Dudestin/tinyEtherDeveloper/RTL_project/L2-Switch/L2-Switch_watcherInst.v

module CW_TOP_WRAPPER(jtdi, jtck, jrstn, jscan, jshift, jupdate, jtdo, non_bus_din, bus_din, trig_clk, wt_ce, wt_en, wt_addr);
	localparam DEFAULT_CTRL_REG_LEN = 298;
	localparam DEFAULT_STAT_REG_LEN = 18;
	localparam DEFAULT_STOP_LEN = 682;
	localparam DEFAULT_NON_BUS_NODE_NUM = 2;
	localparam DEFAULT_BUS_NODE_NUM = 15;
	localparam DEFAULT_BUS_NUM = 4;
	localparam DEFAULT_BUS1_WIDTH = 4;
	localparam DEFAULT_BUS2_WIDTH = 4;
	localparam DEFAULT_BUS3_WIDTH = 4;
	localparam DEFAULT_BUS4_WIDTH = 3;
	input jtdi;
	input jtck;
	input jrstn;
	input [1:0] jscan;
	input jshift;
	input jupdate;
	output [1:0] jtdo;
	input trig_clk;
	input [DEFAULT_NON_BUS_NODE_NUM-1:0] non_bus_din;
	input [DEFAULT_BUS_NODE_NUM-1:0] bus_din;
	output wt_ce;
	output wt_en;
	output [15:0] wt_addr;

	cwc_top #(.BUS1_WIDTH(DEFAULT_BUS1_WIDTH), .BUS2_WIDTH(DEFAULT_BUS2_WIDTH), .BUS3_WIDTH(DEFAULT_BUS3_WIDTH), .BUS4_WIDTH(DEFAULT_BUS4_WIDTH), .CTRL_REG_LEN(DEFAULT_CTRL_REG_LEN), .STAT_REG_LEN(DEFAULT_STAT_REG_LEN), .STOP_LEN(DEFAULT_STOP_LEN), .NON_BUS_NODE_NUM(DEFAULT_NON_BUS_NODE_NUM), .BUS_NODE_NUM(DEFAULT_BUS_NODE_NUM), .BUS_NUM(DEFAULT_BUS_NUM))
	 wrapper_cwc_top(
		.jtdi(jtdi),
		.jtck(jtck),
		.jrstn(jrstn),
		.jscan(jscan),
		.jshift(jshift),
		.jupdate(jupdate),
		.jtdo(jtdo),
		.non_bus_din(non_bus_din),
		.bus_din(bus_din),
		.trig_clk(trig_clk),
		.wt_ce(wt_ce),
		.wt_en(wt_en),
		.wt_addr(wt_addr)
	);
endmodule
