Dudestin/tinyEtherDeveloper/RTL_project/common/al_ip/CTRL_FRAME_RAM_sim.v

// Verilog netlist created by TD v4.4.433
// Thu Aug 11 10:00:17 2022

`timescale 1ns / 1ps
module CTRL_FRAME_FIFO  // al_ip/CTRL_FRAME_FIFO.v(14)
  (
  addra,
  addrb,
  clka,
  clkb,
  dia,
  dib,
  rsta,
  rstb,
  wea,
  web,
  doa,
  dob
  );

  input [9:0] addra;  // al_ip/CTRL_FRAME_FIFO.v(25)
  input [9:0] addrb;  // al_ip/CTRL_FRAME_FIFO.v(26)
  input clka;  // al_ip/CTRL_FRAME_FIFO.v(29)
  input clkb;  // al_ip/CTRL_FRAME_FIFO.v(30)
  input [31:0] dia;  // al_ip/CTRL_FRAME_FIFO.v(23)
  input [31:0] dib;  // al_ip/CTRL_FRAME_FIFO.v(24)
  input rsta;  // al_ip/CTRL_FRAME_FIFO.v(31)
  input rstb;  // al_ip/CTRL_FRAME_FIFO.v(32)
  input [3:0] wea;  // al_ip/CTRL_FRAME_FIFO.v(27)
  input [3:0] web;  // al_ip/CTRL_FRAME_FIFO.v(28)
  output [31:0] doa;  // al_ip/CTRL_FRAME_FIFO.v(19)
  output [31:0] dob;  // al_ip/CTRL_FRAME_FIFO.v(20)


  EG_PHY_CONFIG #(
    .DONE_PERSISTN("ENABLE"),
    .INIT_PERSISTN("ENABLE"),
    .JTAG_PERSISTN("DISABLE"),
    .PROGRAMN_PERSISTN("DISABLE"))
    config_inst ();
  // address_offset=0;data_offset=0;depth=1024;width=8;num_section=1;width_per_section=8;section_size=32;working_depth=1024;working_width=9;address_step=1;bytes_in_per_section=1;
  EG_PHY_BRAM #(
    .CEAMUX("1"),
    .CEBMUX("1"),
    .CSA0("1"),
    .CSA1("1"),
    .CSA2("1"),
    .CSB0("1"),
    .CSB1("1"),
    .CSB2("1"),
    .DATA_WIDTH_A("9"),
    .DATA_WIDTH_B("9"),
    .INITP_00(256'h0000000000000000000000000000000000000000000000000000000000000000),
    .INITP_01(256'h0000000000000000000000000000000000000000000000000000000000000000),
    .INITP_02(256'h0000000000000000000000000000000000000000000000000000000000000000),
    .INITP_03(256'h0000000000000000000000000000000000000000000000000000000000000000),
    .INIT_00(256'h0000000000000000000000000000000000000000000000000000000000000000),
    .INIT_01(256'h0000000000000000000000000000000000000000000000000000000000000000),
    .INIT_02(256'h0000000000000000000000000000000000000000000000000000000000000000),
    .INIT_03(256'h0000000000000000000000000000000000000000000000000000000000000000),
    .INIT_04(256'h0000000000000000000000000000000000000000000000000000000000000000),
    .INIT_05(256'h0000000000000000000000000000000000000000000000000000000000000000),
    .INIT_06(256'h0000000000000000000000000000000000000000000000000000000000000000),
    .INIT_07(256'h0000000000000000000000000000000000000000000000000000000000000000),
    .INIT_08(256'h0000000000000000000000000000000000000000000000000000000000000000),
    .INIT_09(256'h0000000000000000000000000000000000000000000000000000000000000000),
    .INIT_0A(256'h0000000000000000000000000000000000000000000000000000000000000000),
    .INIT_0B(256'h0000000000000000000000000000000000000000000000000000000000000000),
    .INIT_0C(256'h0000000000000000000000000000000000000000000000000000000000000000),
    .INIT_0D(256'h0000000000000000000000000000000000000000000000000000000000000000),
    .INIT_0E(256'h0000000000000000000000000000000000000000000000000000000000000000),
    .INIT_0F(256'h0000000000000000000000000000000000000000000000000000000000000000),
    .INIT_10(256'h0000000000000000000000000000000000000000000000000000000000000000),
    .INIT_11(256'h0000000000000000000000000000000000000000000000000000000000000000),
    .INIT_12(256'h0000000000000000000000000000000000000000000000000000000000000000),
    .INIT_13(256'h0000000000000000000000000000000000000000000000000000000000000000),
    .INIT_14(256'h0000000000000000000000000000000000000000000000000000000000000000),
    .INIT_15(256'h0000000000000000000000000000000000000000000000000000000000000000),
    .INIT_16(256'h0000000000000000000000000000000000000000000000000000000000000000),
    .INIT_17(256'h0000000000000000000000000000000000000000000000000000000000000000),
    .INIT_18(256'h0000000000000000000000000000000000000000000000000000000000000000),
    .INIT_19(256'h0000000000000000000000000000000000000000000000000000000000000000),
    .INIT_1A(256'h0000000000000000000000000000000000000000000000000000000000000000),
    .INIT_1B(256'h0000000000000000000000000000000000000000000000000000000000000000),
    .INIT_1C(256'h0000000000000000000000000000000000000000000000000000000000000000),
    .INIT_1D(256'h0000000000000000000000000000000000000000000000000000000000000000),
    .INIT_1E(256'h0000000000000000000000000000000000000000000000000000000000000000),
    .INIT_1F(256'h0000000000000000000000000000000000000000000000000000000000000000),
    .MODE("DP8K"),
    .OCEAMUX("0"),
    .OCEBMUX("0"),
    .REGMODE_A("NOREG"),
    .REGMODE_B("NOREG"),
    .RESETMODE("SYNC"),
    .WRITEMODE_A("NORMAL"),
    .WRITEMODE_B("NORMAL"))
    inst_1024x32_sub_000000_000 (
    .addra({addra,3'b111}),
    .addrb({addrb,3'b111}),
    .clka(clka),
    .clkb(clkb),
    .dia({open_n55,dia[7:0]}),
    .dib({open_n56,dib[7:0]}),
    .rsta(rsta),
    .rstb(rstb),
    .wea(wea[0]),
    .web(web[0]),
    .doa({open_n59,doa[7:0]}),
    .dob({open_n60,dob[7:0]}));
  // address_offset=0;data_offset=8;depth=1024;width=8;num_section=1;width_per_section=8;section_size=32;working_depth=1024;working_width=9;address_step=1;bytes_in_per_section=1;
  EG_PHY_BRAM #(
    .CEAMUX("1"),
    .CEBMUX("1"),
    .CSA0("1"),
    .CSA1("1"),
    .CSA2("1"),
    .CSB0("1"),
    .CSB1("1"),
    .CSB2("1"),
    .DATA_WIDTH_A("9"),
    .DATA_WIDTH_B("9"),
    .INITP_00(256'h0000000000000000000000000000000000000000000000000000000000000000),
    .INITP_01(256'h0000000000000000000000000000000000000000000000000000000000000000),
    .INITP_02(256'h0000000000000000000000000000000000000000000000000000000000000000),
    .INITP_03(256'h0000000000000000000000000000000000000000000000000000000000000000),
    .INIT_00(256'h0000000000000000000000000000000000000000000000000000000000000000),
    .INIT_01(256'h0000000000000000000000000000000000000000000000000000000000000000),
    .INIT_02(256'h0000000000000000000000000000000000000000000000000000000000000000),
    .INIT_03(256'h0000000000000000000000000000000000000000000000000000000000000000),
    .INIT_04(256'h0000000000000000000000000000000000000000000000000000000000000000),
    .INIT_05(256'h0000000000000000000000000000000000000000000000000000000000000000),
    .INIT_06(256'h0000000000000000000000000000000000000000000000000000000000000000),
    .INIT_07(256'h0000000000000000000000000000000000000000000000000000000000000000),
    .INIT_08(256'h0000000000000000000000000000000000000000000000000000000000000000),
    .INIT_09(256'h0000000000000000000000000000000000000000000000000000000000000000),
    .INIT_0A(256'h0000000000000000000000000000000000000000000000000000000000000000),
    .INIT_0B(256'h0000000000000000000000000000000000000000000000000000000000000000),
    .INIT_0C(256'h0000000000000000000000000000000000000000000000000000000000000000),
    .INIT_0D(256'h0000000000000000000000000000000000000000000000000000000000000000),
    .INIT_0E(256'h0000000000000000000000000000000000000000000000000000000000000000),
    .INIT_0F(256'h0000000000000000000000000000000000000000000000000000000000000000),
    .INIT_10(256'h0000000000000000000000000000000000000000000000000000000000000000),
    .INIT_11(256'h0000000000000000000000000000000000000000000000000000000000000000),
    .INIT_12(256'h0000000000000000000000000000000000000000000000000000000000000000),
    .INIT_13(256'h0000000000000000000000000000000000000000000000000000000000000000),
    .INIT_14(256'h0000000000000000000000000000000000000000000000000000000000000000),
    .INIT_15(256'h0000000000000000000000000000000000000000000000000000000000000000),
    .INIT_16(256'h0000000000000000000000000000000000000000000000000000000000000000),
    .INIT_17(256'h0000000000000000000000000000000000000000000000000000000000000000),
    .INIT_18(256'h0000000000000000000000000000000000000000000000000000000000000000),
    .INIT_19(256'h0000000000000000000000000000000000000000000000000000000000000000),
    .INIT_1A(256'h0000000000000000000000000000000000000000000000000000000000000000),
    .INIT_1B(256'h0000000000000000000000000000000000000000000000000000000000000000),
    .INIT_1C(256'h0000000000000000000000000000000000000000000000000000000000000000),
    .INIT_1D(256'h0000000000000000000000000000000000000000000000000000000000000000),
    .INIT_1E(256'h0000000000000000000000000000000000000000000000000000000000000000),
    .INIT_1F(256'h0000000000000000000000000000000000000000000000000000000000000000),
    .MODE("DP8K"),
    .OCEAMUX("0"),
    .OCEBMUX("0"),
    .REGMODE_A("NOREG"),
    .REGMODE_B("NOREG"),
    .RESETMODE("SYNC"),
    .WRITEMODE_A("NORMAL"),
    .WRITEMODE_B("NORMAL"))
    inst_1024x32_sub_000000_008 (
    .addra({addra,3'b111}),
    .addrb({addrb,3'b111}),
    .clka(clka),
    .clkb(clkb),
    .dia({open_n69,dia[15:8]}),
    .dib({open_n70,dib[15:8]}),
    .rsta(rsta),
    .rstb(rstb),
    .wea(wea[1]),
    .web(web[1]),
    .doa({open_n73,doa[15:8]}),
    .dob({open_n74,dob[15:8]}));
  // address_offset=0;data_offset=16;depth=1024;width=8;num_section=1;width_per_section=8;section_size=32;working_depth=1024;working_width=9;address_step=1;bytes_in_per_section=1;
  EG_PHY_BRAM #(
    .CEAMUX("1"),
    .CEBMUX("1"),
    .CSA0("1"),
    .CSA1("1"),
    .CSA2("1"),
    .CSB0("1"),
    .CSB1("1"),
    .CSB2("1"),
    .DATA_WIDTH_A("9"),
    .DATA_WIDTH_B("9"),
    .INITP_00(256'h0000000000000000000000000000000000000000000000000000000000000000),
    .INITP_01(256'h0000000000000000000000000000000000000000000000000000000000000000),
    .INITP_02(256'h0000000000000000000000000000000000000000000000000000000000000000),
    .INITP_03(256'h0000000000000000000000000000000000000000000000000000000000000000),
    .INIT_00(256'h0000000000000000000000000000000000000000000000000000000000000000),
    .INIT_01(256'h0000000000000000000000000000000000000000000000000000000000000000),
    .INIT_02(256'h0000000000000000000000000000000000000000000000000000000000000000),
    .INIT_03(256'h0000000000000000000000000000000000000000000000000000000000000000),
    .INIT_04(256'h0000000000000000000000000000000000000000000000000000000000000000),
    .INIT_05(256'h0000000000000000000000000000000000000000000000000000000000000000),
    .INIT_06(256'h0000000000000000000000000000000000000000000000000000000000000000),
    .INIT_07(256'h0000000000000000000000000000000000000000000000000000000000000000),
    .INIT_08(256'h0000000000000000000000000000000000000000000000000000000000000000),
    .INIT_09(256'h0000000000000000000000000000000000000000000000000000000000000000),
    .INIT_0A(256'h0000000000000000000000000000000000000000000000000000000000000000),
    .INIT_0B(256'h0000000000000000000000000000000000000000000000000000000000000000),
    .INIT_0C(256'h0000000000000000000000000000000000000000000000000000000000000000),
    .INIT_0D(256'h0000000000000000000000000000000000000000000000000000000000000000),
    .INIT_0E(256'h0000000000000000000000000000000000000000000000000000000000000000),
    .INIT_0F(256'h0000000000000000000000000000000000000000000000000000000000000000),
    .INIT_10(256'h0000000000000000000000000000000000000000000000000000000000000000),
    .INIT_11(256'h0000000000000000000000000000000000000000000000000000000000000000),
    .INIT_12(256'h0000000000000000000000000000000000000000000000000000000000000000),
    .INIT_13(256'h0000000000000000000000000000000000000000000000000000000000000000),
    .INIT_14(256'h0000000000000000000000000000000000000000000000000000000000000000),
    .INIT_15(256'h0000000000000000000000000000000000000000000000000000000000000000),
    .INIT_16(256'h0000000000000000000000000000000000000000000000000000000000000000),
    .INIT_17(256'h0000000000000000000000000000000000000000000000000000000000000000),
    .INIT_18(256'h0000000000000000000000000000000000000000000000000000000000000000),
    .INIT_19(256'h0000000000000000000000000000000000000000000000000000000000000000),
    .INIT_1A(256'h0000000000000000000000000000000000000000000000000000000000000000),
    .INIT_1B(256'h0000000000000000000000000000000000000000000000000000000000000000),
    .INIT_1C(256'h0000000000000000000000000000000000000000000000000000000000000000),
    .INIT_1D(256'h0000000000000000000000000000000000000000000000000000000000000000),
    .INIT_1E(256'h0000000000000000000000000000000000000000000000000000000000000000),
    .INIT_1F(256'h0000000000000000000000000000000000000000000000000000000000000000),
    .MODE("DP8K"),
    .OCEAMUX("0"),
    .OCEBMUX("0"),
    .REGMODE_A("NOREG"),
    .REGMODE_B("NOREG"),
    .RESETMODE("SYNC"),
    .WRITEMODE_A("NORMAL"),
    .WRITEMODE_B("NORMAL"))
    inst_1024x32_sub_000000_016 (
    .addra({addra,3'b111}),
    .addrb({addrb,3'b111}),
    .clka(clka),
    .clkb(clkb),
    .dia({open_n83,dia[23:16]}),
    .dib({open_n84,dib[23:16]}),
    .rsta(rsta),
    .rstb(rstb),
    .wea(wea[2]),
    .web(web[2]),
    .doa({open_n87,doa[23:16]}),
    .dob({open_n88,dob[23:16]}));
  // address_offset=0;data_offset=24;depth=1024;width=8;num_section=1;width_per_section=8;section_size=32;working_depth=1024;working_width=9;address_step=1;bytes_in_per_section=1;
  EG_PHY_BRAM #(
    .CEAMUX("1"),
    .CEBMUX("1"),
    .CSA0("1"),
    .CSA1("1"),
    .CSA2("1"),
    .CSB0("1"),
    .CSB1("1"),
    .CSB2("1"),
    .DATA_WIDTH_A("9"),
    .DATA_WIDTH_B("9"),
    .INITP_00(256'h0000000000000000000000000000000000000000000000000000000000000000),
    .INITP_01(256'h0000000000000000000000000000000000000000000000000000000000000000),
    .INITP_02(256'h0000000000000000000000000000000000000000000000000000000000000000),
    .INITP_03(256'h0000000000000000000000000000000000000000000000000000000000000000),
    .INIT_00(256'h0000000000000000000000000000000000000000000000000000000000000000),
    .INIT_01(256'h0000000000000000000000000000000000000000000000000000000000000000),
    .INIT_02(256'h0000000000000000000000000000000000000000000000000000000000000000),
    .INIT_03(256'h0000000000000000000000000000000000000000000000000000000000000000),
    .INIT_04(256'h0000000000000000000000000000000000000000000000000000000000000000),
    .INIT_05(256'h0000000000000000000000000000000000000000000000000000000000000000),
    .INIT_06(256'h0000000000000000000000000000000000000000000000000000000000000000),
    .INIT_07(256'h0000000000000000000000000000000000000000000000000000000000000000),
    .INIT_08(256'h0000000000000000000000000000000000000000000000000000000000000000),
    .INIT_09(256'h0000000000000000000000000000000000000000000000000000000000000000),
    .INIT_0A(256'h0000000000000000000000000000000000000000000000000000000000000000),
    .INIT_0B(256'h0000000000000000000000000000000000000000000000000000000000000000),
    .INIT_0C(256'h0000000000000000000000000000000000000000000000000000000000000000),
    .INIT_0D(256'h0000000000000000000000000000000000000000000000000000000000000000),
    .INIT_0E(256'h0000000000000000000000000000000000000000000000000000000000000000),
    .INIT_0F(256'h0000000000000000000000000000000000000000000000000000000000000000),
    .INIT_10(256'h0000000000000000000000000000000000000000000000000000000000000000),
    .INIT_11(256'h0000000000000000000000000000000000000000000000000000000000000000),
    .INIT_12(256'h0000000000000000000000000000000000000000000000000000000000000000),
    .INIT_13(256'h0000000000000000000000000000000000000000000000000000000000000000),
    .INIT_14(256'h0000000000000000000000000000000000000000000000000000000000000000),
    .INIT_15(256'h0000000000000000000000000000000000000000000000000000000000000000),
    .INIT_16(256'h0000000000000000000000000000000000000000000000000000000000000000),
    .INIT_17(256'h0000000000000000000000000000000000000000000000000000000000000000),
    .INIT_18(256'h0000000000000000000000000000000000000000000000000000000000000000),
    .INIT_19(256'h0000000000000000000000000000000000000000000000000000000000000000),
    .INIT_1A(256'h0000000000000000000000000000000000000000000000000000000000000000),
    .INIT_1B(256'h0000000000000000000000000000000000000000000000000000000000000000),
    .INIT_1C(256'h0000000000000000000000000000000000000000000000000000000000000000),
    .INIT_1D(256'h0000000000000000000000000000000000000000000000000000000000000000),
    .INIT_1E(256'h0000000000000000000000000000000000000000000000000000000000000000),
    .INIT_1F(256'h0000000000000000000000000000000000000000000000000000000000000000),
    .MODE("DP8K"),
    .OCEAMUX("0"),
    .OCEBMUX("0"),
    .REGMODE_A("NOREG"),
    .REGMODE_B("NOREG"),
    .RESETMODE("SYNC"),
    .WRITEMODE_A("NORMAL"),
    .WRITEMODE_B("NORMAL"))
    inst_1024x32_sub_000000_024 (
    .addra({addra,3'b111}),
    .addrb({addrb,3'b111}),
    .clka(clka),
    .clkb(clkb),
    .dia({open_n97,dia[31:24]}),
    .dib({open_n98,dib[31:24]}),
    .rsta(rsta),
    .rstb(rstb),
    .wea(wea[3]),
    .web(web[3]),
    .doa({open_n101,doa[31:24]}),
    .dob({open_n102,dob[31:24]}));

endmodule 
