Dudestin/tinyEtherDeveloper/RTL_project/common/al_ip/bram32k_sim.v

// Verilog netlist created by TD v4.4.433
// Tue Jul 26 14:06:52 2022

`timescale 1ns / 1ps
module bram32k  // al_ip/bram32k.v(14)
  (
  addra,
  addrb,
  clka,
  clkb,
  dia,
  dib,
  rsta,
  rstb,
  wea,
  web,
  doa,
  dob
  );

  input [11:0] addra;  // al_ip/bram32k.v(25)
  input [11:0] addrb;  // al_ip/bram32k.v(26)
  input clka;  // al_ip/bram32k.v(29)
  input clkb;  // al_ip/bram32k.v(30)
  input [7:0] dia;  // al_ip/bram32k.v(23)
  input [7:0] dib;  // al_ip/bram32k.v(24)
  input rsta;  // al_ip/bram32k.v(31)
  input rstb;  // al_ip/bram32k.v(32)
  input wea;  // al_ip/bram32k.v(27)
  input web;  // al_ip/bram32k.v(28)
  output [7:0] doa;  // al_ip/bram32k.v(19)
  output [7:0] dob;  // al_ip/bram32k.v(20)


  EG_PHY_CONFIG #(
    .DONE_PERSISTN("ENABLE"),
    .INIT_PERSISTN("ENABLE"),
    .JTAG_PERSISTN("DISABLE"),
    .PROGRAMN_PERSISTN("DISABLE"))
    config_inst ();
  // address_offset=0;data_offset=0;depth=4096;width=8;num_section=1;width_per_section=8;section_size=8;working_depth=4096;working_width=8;address_step=1;bytes_in_per_section=1;
  EG_PHY_BRAM32K #(
    .CSAMUX("1"),
    .CSBMUX("1"),
    .DATA_WIDTH_A("8"),
    .DATA_WIDTH_B("8"),
    .INIT_00(256'h0000000000000000000000000000000000000000000000000000000000000000),
    .INIT_01(256'h0000000000000000000000000000000000000000000000000000000000000000),
    .INIT_02(256'h0000000000000000000000000000000000000000000000000000000000000000),
    .INIT_03(256'h0000000000000000000000000000000000000000000000000000000000000000),
    .INIT_04(256'h0000000000000000000000000000000000000000000000000000000000000000),
    .INIT_05(256'h0000000000000000000000000000000000000000000000000000000000000000),
    .INIT_06(256'h0000000000000000000000000000000000000000000000000000000000000000),
    .INIT_07(256'h0000000000000000000000000000000000000000000000000000000000000000),
    .INIT_08(256'h0000000000000000000000000000000000000000000000000000000000000000),
    .INIT_09(256'h0000000000000000000000000000000000000000000000000000000000000000),
    .INIT_0A(256'h0000000000000000000000000000000000000000000000000000000000000000),
    .INIT_0B(256'h0000000000000000000000000000000000000000000000000000000000000000),
    .INIT_0C(256'h0000000000000000000000000000000000000000000000000000000000000000),
    .INIT_0D(256'h0000000000000000000000000000000000000000000000000000000000000000),
    .INIT_0E(256'h0000000000000000000000000000000000000000000000000000000000000000),
    .INIT_0F(256'h0000000000000000000000000000000000000000000000000000000000000000),
    .INIT_10(256'h0000000000000000000000000000000000000000000000000000000000000000),
    .INIT_11(256'h0000000000000000000000000000000000000000000000000000000000000000),
    .INIT_12(256'h0000000000000000000000000000000000000000000000000000000000000000),
    .INIT_13(256'h0000000000000000000000000000000000000000000000000000000000000000),
    .INIT_14(256'h0000000000000000000000000000000000000000000000000000000000000000),
    .INIT_15(256'h0000000000000000000000000000000000000000000000000000000000000000),
    .INIT_16(256'h0000000000000000000000000000000000000000000000000000000000000000),
    .INIT_17(256'h0000000000000000000000000000000000000000000000000000000000000000),
    .INIT_18(256'h0000000000000000000000000000000000000000000000000000000000000000),
    .INIT_19(256'h0000000000000000000000000000000000000000000000000000000000000000),
    .INIT_1A(256'h0000000000000000000000000000000000000000000000000000000000000000),
    .INIT_1B(256'h0000000000000000000000000000000000000000000000000000000000000000),
    .INIT_1C(256'h0000000000000000000000000000000000000000000000000000000000000000),
    .INIT_1D(256'h0000000000000000000000000000000000000000000000000000000000000000),
    .INIT_1E(256'h0000000000000000000000000000000000000000000000000000000000000000),
    .INIT_1F(256'h0000000000000000000000000000000000000000000000000000000000000000),
    .INIT_20(256'h0000000000000000000000000000000000000000000000000000000000000000),
    .INIT_21(256'h0000000000000000000000000000000000000000000000000000000000000000),
    .INIT_22(256'h0000000000000000000000000000000000000000000000000000000000000000),
    .INIT_23(256'h0000000000000000000000000000000000000000000000000000000000000000),
    .INIT_24(256'h0000000000000000000000000000000000000000000000000000000000000000),
    .INIT_25(256'h0000000000000000000000000000000000000000000000000000000000000000),
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
    .INIT_7B(256'h0000000000000000000000000000000000000000000000000000000000000000),
    .INIT_7C(256'h0000000000000000000000000000000000000000000000000000000000000000),
    .INIT_7D(256'h0000000000000000000000000000000000000000000000000000000000000000),
    .INIT_7E(256'h0000000000000000000000000000000000000000000000000000000000000000),
    .INIT_7F(256'h0000000000000000000000000000000000000000000000000000000000000000),
    .MODE("DP16K"),
    .OCEAMUX("1"),
    .OCEBMUX("1"),
    .REGMODE_A("OUTREG"),
    .REGMODE_B("OUTREG"),
    .SRMODE("SYNC"),
    .WRITEMODE_A("NORMAL"),
    .WRITEMODE_B("NORMAL"))
    inst_4096x8_sub_000000_000 (
    .addra(addra[11:1]),
    .addrb(addrb[11:1]),
    .bytea(addra[0]),
    .byteb(addrb[0]),
    .clka(clka),
    .clkb(clkb),
    .dia({open_n51,open_n52,open_n53,open_n54,open_n55,open_n56,open_n57,open_n58,dia}),
    .dib({open_n59,open_n60,open_n61,open_n62,open_n63,open_n64,open_n65,open_n66,dib}),
    .rsta(rsta),
    .rstb(rstb),
    .wea(wea),
    .web(web),
    .doa({open_n69,open_n70,open_n71,open_n72,open_n73,open_n74,open_n75,open_n76,doa}),
    .dob({open_n77,open_n78,open_n79,open_n80,open_n81,open_n82,open_n83,open_n84,dob}));

endmodule 
