Dudestin/tinyEtherDeveloper/RTL_project/common/al_ip/ram_dp_ip_sim.v

// Verilog netlist created by TD v4.4.433
// Sat Jul 23 10:05:43 2022

`timescale 1ns / 1ps
module ram_dp_ip  // al_ip/ram_dp_ip.v(14)
  (
  addra,
  addrb,
  clka,
  clkb,
  dia,
  dib,
  rsta,
  rstb,
  wea,
  web,
  doa,
  dob
  );

  input [9:0] addra;  // al_ip/ram_dp_ip.v(25)
  input [9:0] addrb;  // al_ip/ram_dp_ip.v(26)
  input clka;  // al_ip/ram_dp_ip.v(29)
  input clkb;  // al_ip/ram_dp_ip.v(30)
  input [31:0] dia;  // al_ip/ram_dp_ip.v(23)
  input [31:0] dib;  // al_ip/ram_dp_ip.v(24)
  input rsta;  // al_ip/ram_dp_ip.v(31)
  input rstb;  // al_ip/ram_dp_ip.v(32)
  input wea;  // al_ip/ram_dp_ip.v(27)
  input web;  // al_ip/ram_dp_ip.v(28)
  output [31:0] doa;  // al_ip/ram_dp_ip.v(19)
  output [31:0] dob;  // al_ip/ram_dp_ip.v(20)


  EG_PHY_CONFIG #(
    .DONE_PERSISTN("ENABLE"),
    .INIT_PERSISTN("ENABLE"),
    .JTAG_PERSISTN("DISABLE"),
    .PROGRAMN_PERSISTN("DISABLE"))
    config_inst ();
  // address_offset=0;data_offset=0;depth=1024;width=9;num_section=1;width_per_section=9;section_size=32;working_depth=1024;working_width=9;address_step=1;bytes_in_per_section=1;
  EG_PHY_BRAM #(
    .CEAMUX("1"),
    .CEBMUX("1"),
    .CSA0("1"),
    .CSA1("1"),
    .CSA2("1"),
    .CSB0("1"),
    .CSB1("1"),
    .CSB2("1"),
    .DATA_WIDTH_A("9"),
    .DATA_WIDTH_B("9"),
    .INITP_00(256'h0000000000000000000000000000000000000000000000000000000000000000),
    .INITP_01(256'h0000000000000000000000000000000000000000000000000000000000000000),
    .INITP_02(256'h0000000000000000000000000000000000000000000000000000000000000000),
    .INITP_03(256'h0000000000000000000000000000000000000000000000000000000000000000),
    .INIT_00(256'h0000000000000000000000000000000000000000000000000000000000000000),
    .INIT_01(256'h0000000000000000000000000000000000000000000000000000000000000000),
    .INIT_02(256'h0000000000000000000000000000000000000000000000000000000000000000),
    .INIT_03(256'h0000000000000000000000000000000000000000000000000000000000000000),
    .INIT_04(256'h0000000000000000000000000000000000000000000000000000000000000000),
    .INIT_05(256'h0000000000000000000000000000000000000000000000000000000000000000),
    .INIT_06(256'h0000000000000000000000000000000000000000000000000000000000000000),
    .INIT_07(256'h0000000000000000000000000000000000000000000000000000000000000000),
    .INIT_08(256'h0000000000000000000000000000000000000000000000000000000000000000),
    .INIT_09(256'h0000000000000000000000000000000000000000000000000000000000000000),
    .INIT_0A(256'h0000000000000000000000000000000000000000000000000000000000000000),
    .INIT_0B(256'h0000000000000000000000000000000000000000000000000000000000000000),
    .INIT_0C(256'h0000000000000000000000000000000000000000000000000000000000000000),
    .INIT_0D(256'h0000000000000000000000000000000000000000000000000000000000000000),
    .INIT_0E(256'h0000000000000000000000000000000000000000000000000000000000000000),
    .INIT_0F(256'h0000000000000000000000000000000000000000000000000000000000000000),
    .INIT_10(256'h0000000000000000000000000000000000000000000000000000000000000000),
    .INIT_11(256'h0000000000000000000000000000000000000000000000000000000000000000),
    .INIT_12(256'h0000000000000000000000000000000000000000000000000000000000000000),
    .INIT_13(256'h0000000000000000000000000000000000000000000000000000000000000000),
    .INIT_14(256'h0000000000000000000000000000000000000000000000000000000000000000),
    .INIT_15(256'h0000000000000000000000000000000000000000000000000000000000000000),
    .INIT_16(256'h0000000000000000000000000000000000000000000000000000000000000000),
    .INIT_17(256'h0000000000000000000000000000000000000000000000000000000000000000),
    .INIT_18(256'h0000000000000000000000000000000000000000000000000000000000000000),
    .INIT_19(256'h0000000000000000000000000000000000000000000000000000000000000000),
    .INIT_1A(256'h0000000000000000000000000000000000000000000000000000000000000000),
    .INIT_1B(256'h0000000000000000000000000000000000000000000000000000000000000000),
    .INIT_1C(256'h0000000000000000000000000000000000000000000000000000000000000000),
    .INIT_1D(256'h0000000000000000000000000000000000000000000000000000000000000000),
    .INIT_1E(256'h0000000000000000000000000000000000000000000000000000000000000000),
    .INIT_1F(256'h0000000000000000000000000000000000000000000000000000000000000000),
    .MODE("DP8K"),
    .OCEAMUX("0"),
    .OCEBMUX("0"),
    .REGMODE_A("NOREG"),
    .REGMODE_B("NOREG"),
    .RESETMODE("SYNC"),
    .WRITEMODE_A("WRITETHROUGH"),
    .WRITEMODE_B("WRITETHROUGH"))
    inst_1024x32_sub_000000_000 (
    .addra({addra,3'b111}),
    .addrb({addrb,3'b111}),
    .clka(clka),
    .clkb(clkb),
    .dia(dia[8:0]),
    .dib(dib[8:0]),
    .rsta(rsta),
    .rstb(rstb),
    .wea(wea),
    .web(web),
    .doa(doa[8:0]),
    .dob(dob[8:0]));
  // address_offset=0;data_offset=9;depth=1024;width=9;num_section=1;width_per_section=9;section_size=32;working_depth=1024;working_width=9;address_step=1;bytes_in_per_section=1;
  EG_PHY_BRAM #(
    .CEAMUX("1"),
    .CEBMUX("1"),
    .CSA0("1"),
    .CSA1("1"),
    .CSA2("1"),
    .CSB0("1"),
    .CSB1("1"),
    .CSB2("1"),
    .DATA_WIDTH_A("9"),
    .DATA_WIDTH_B("9"),
    .INITP_00(256'h0000000000000000000000000000000000000000000000000000000000000000),
    .INITP_01(256'h0000000000000000000000000000000000000000000000000000000000000000),
    .INITP_02(256'h0000000000000000000000000000000000000000000000000000000000000000),
    .INITP_03(256'h0000000000000000000000000000000000000000000000000000000000000000),
    .INIT_00(256'h0000000000000000000000000000000000000000000000000000000000000000),
    .INIT_01(256'h0000000000000000000000000000000000000000000000000000000000000000),
    .INIT_02(256'h0000000000000000000000000000000000000000000000000000000000000000),
    .INIT_03(256'h0000000000000000000000000000000000000000000000000000000000000000),
    .INIT_04(256'h0000000000000000000000000000000000000000000000000000000000000000),
    .INIT_05(256'h0000000000000000000000000000000000000000000000000000000000000000),
    .INIT_06(256'h0000000000000000000000000000000000000000000000000000000000000000),
    .INIT_07(256'h0000000000000000000000000000000000000000000000000000000000000000),
    .INIT_08(256'h0000000000000000000000000000000000000000000000000000000000000000),
    .INIT_09(256'h0000000000000000000000000000000000000000000000000000000000000000),
    .INIT_0A(256'h0000000000000000000000000000000000000000000000000000000000000000),
    .INIT_0B(256'h0000000000000000000000000000000000000000000000000000000000000000),
    .INIT_0C(256'h0000000000000000000000000000000000000000000000000000000000000000),
    .INIT_0D(256'h0000000000000000000000000000000000000000000000000000000000000000),
    .INIT_0E(256'h0000000000000000000000000000000000000000000000000000000000000000),
    .INIT_0F(256'h0000000000000000000000000000000000000000000000000000000000000000),
    .INIT_10(256'h0000000000000000000000000000000000000000000000000000000000000000),
    .INIT_11(256'h0000000000000000000000000000000000000000000000000000000000000000),
    .INIT_12(256'h0000000000000000000000000000000000000000000000000000000000000000),
    .INIT_13(256'h0000000000000000000000000000000000000000000000000000000000000000),
    .INIT_14(256'h0000000000000000000000000000000000000000000000000000000000000000),
    .INIT_15(256'h0000000000000000000000000000000000000000000000000000000000000000),
    .INIT_16(256'h0000000000000000000000000000000000000000000000000000000000000000),
    .INIT_17(256'h0000000000000000000000000000000000000000000000000000000000000000),
    .INIT_18(256'h0000000000000000000000000000000000000000000000000000000000000000),
    .INIT_19(256'h0000000000000000000000000000000000000000000000000000000000000000),
    .INIT_1A(256'h0000000000000000000000000000000000000000000000000000000000000000),
    .INIT_1B(256'h0000000000000000000000000000000000000000000000000000000000000000),
    .INIT_1C(256'h0000000000000000000000000000000000000000000000000000000000000000),
    .INIT_1D(256'h0000000000000000000000000000000000000000000000000000000000000000),
    .INIT_1E(256'h0000000000000000000000000000000000000000000000000000000000000000),
    .INIT_1F(256'h0000000000000000000000000000000000000000000000000000000000000000),
    .MODE("DP8K"),
    .OCEAMUX("0"),
    .OCEBMUX("0"),
    .REGMODE_A("NOREG"),
    .REGMODE_B("NOREG"),
    .RESETMODE("SYNC"),
    .WRITEMODE_A("WRITETHROUGH"),
    .WRITEMODE_B("WRITETHROUGH"))
    inst_1024x32_sub_000000_009 (
    .addra({addra,3'b111}),
    .addrb({addrb,3'b111}),
    .clka(clka),
    .clkb(clkb),
    .dia(dia[17:9]),
    .dib(dib[17:9]),
    .rsta(rsta),
    .rstb(rstb),
    .wea(wea),
    .web(web),
    .doa(doa[17:9]),
    .dob(dob[17:9]));
  // address_offset=0;data_offset=18;depth=1024;width=9;num_section=1;width_per_section=9;section_size=32;working_depth=1024;working_width=9;address_step=1;bytes_in_per_section=1;
  EG_PHY_BRAM #(
    .CEAMUX("1"),
    .CEBMUX("1"),
    .CSA0("1"),
    .CSA1("1"),
    .CSA2("1"),
    .CSB0("1"),
    .CSB1("1"),
    .CSB2("1"),
    .DATA_WIDTH_A("9"),
    .DATA_WIDTH_B("9"),
    .INITP_00(256'h0000000000000000000000000000000000000000000000000000000000000000),
    .INITP_01(256'h0000000000000000000000000000000000000000000000000000000000000000),
    .INITP_02(256'h0000000000000000000000000000000000000000000000000000000000000000),
    .INITP_03(256'h0000000000000000000000000000000000000000000000000000000000000000),
    .INIT_00(256'h0000000000000000000000000000000000000000000000000000000000000000),
    .INIT_01(256'h0000000000000000000000000000000000000000000000000000000000000000),
    .INIT_02(256'h0000000000000000000000000000000000000000000000000000000000000000),
    .INIT_03(256'h0000000000000000000000000000000000000000000000000000000000000000),
    .INIT_04(256'h0000000000000000000000000000000000000000000000000000000000000000),
    .INIT_05(256'h0000000000000000000000000000000000000000000000000000000000000000),
    .INIT_06(256'h0000000000000000000000000000000000000000000000000000000000000000),
    .INIT_07(256'h0000000000000000000000000000000000000000000000000000000000000000),
    .INIT_08(256'h0000000000000000000000000000000000000000000000000000000000000000),
    .INIT_09(256'h0000000000000000000000000000000000000000000000000000000000000000),
    .INIT_0A(256'h0000000000000000000000000000000000000000000000000000000000000000),
    .INIT_0B(256'h0000000000000000000000000000000000000000000000000000000000000000),
    .INIT_0C(256'h0000000000000000000000000000000000000000000000000000000000000000),
    .INIT_0D(256'h0000000000000000000000000000000000000000000000000000000000000000),
    .INIT_0E(256'h0000000000000000000000000000000000000000000000000000000000000000),
    .INIT_0F(256'h0000000000000000000000000000000000000000000000000000000000000000),
    .INIT_10(256'h0000000000000000000000000000000000000000000000000000000000000000),
    .INIT_11(256'h0000000000000000000000000000000000000000000000000000000000000000),
    .INIT_12(256'h0000000000000000000000000000000000000000000000000000000000000000),
    .INIT_13(256'h0000000000000000000000000000000000000000000000000000000000000000),
    .INIT_14(256'h0000000000000000000000000000000000000000000000000000000000000000),
    .INIT_15(256'h0000000000000000000000000000000000000000000000000000000000000000),
    .INIT_16(256'h0000000000000000000000000000000000000000000000000000000000000000),
    .INIT_17(256'h0000000000000000000000000000000000000000000000000000000000000000),
    .INIT_18(256'h0000000000000000000000000000000000000000000000000000000000000000),
    .INIT_19(256'h0000000000000000000000000000000000000000000000000000000000000000),
    .INIT_1A(256'h0000000000000000000000000000000000000000000000000000000000000000),
    .INIT_1B(256'h0000000000000000000000000000000000000000000000000000000000000000),
    .INIT_1C(256'h0000000000000000000000000000000000000000000000000000000000000000),
    .INIT_1D(256'h0000000000000000000000000000000000000000000000000000000000000000),
    .INIT_1E(256'h0000000000000000000000000000000000000000000000000000000000000000),
    .INIT_1F(256'h0000000000000000000000000000000000000000000000000000000000000000),
    .MODE("DP8K"),
    .OCEAMUX("0"),
    .OCEBMUX("0"),
    .REGMODE_A("NOREG"),
    .REGMODE_B("NOREG"),
    .RESETMODE("SYNC"),
    .WRITEMODE_A("WRITETHROUGH"),
    .WRITEMODE_B("WRITETHROUGH"))
    inst_1024x32_sub_000000_018 (
    .addra({addra,3'b111}),
    .addrb({addrb,3'b111}),
    .clka(clka),
    .clkb(clkb),
    .dia(dia[26:18]),
    .dib(dib[26:18]),
    .rsta(rsta),
    .rstb(rstb),
    .wea(wea),
    .web(web),
    .doa(doa[26:18]),
    .dob(dob[26:18]));
  // address_offset=0;data_offset=27;depth=1024;width=5;num_section=1;width_per_section=5;section_size=32;working_depth=1024;working_width=9;address_step=1;bytes_in_per_section=1;
  EG_PHY_BRAM #(
    .CEAMUX("1"),
    .CEBMUX("1"),
    .CSA0("1"),
    .CSA1("1"),
    .CSA2("1"),
    .CSB0("1"),
    .CSB1("1"),
    .CSB2("1"),
    .DATA_WIDTH_A("9"),
    .DATA_WIDTH_B("9"),
    .INITP_00(256'h0000000000000000000000000000000000000000000000000000000000000000),
    .INITP_01(256'h0000000000000000000000000000000000000000000000000000000000000000),
    .INITP_02(256'h0000000000000000000000000000000000000000000000000000000000000000),
    .INITP_03(256'h0000000000000000000000000000000000000000000000000000000000000000),
    .INIT_00(256'h0000000000000000000000000000000000000000000000000000000000000000),
    .INIT_01(256'h0000000000000000000000000000000000000000000000000000000000000000),
    .INIT_02(256'h0000000000000000000000000000000000000000000000000000000000000000),
    .INIT_03(256'h0000000000000000000000000000000000000000000000000000000000000000),
    .INIT_04(256'h0000000000000000000000000000000000000000000000000000000000000000),
    .INIT_05(256'h0000000000000000000000000000000000000000000000000000000000000000),
    .INIT_06(256'h0000000000000000000000000000000000000000000000000000000000000000),
    .INIT_07(256'h0000000000000000000000000000000000000000000000000000000000000000),
    .INIT_08(256'h0000000000000000000000000000000000000000000000000000000000000000),
    .INIT_09(256'h0000000000000000000000000000000000000000000000000000000000000000),
    .INIT_0A(256'h0000000000000000000000000000000000000000000000000000000000000000),
    .INIT_0B(256'h0000000000000000000000000000000000000000000000000000000000000000),
    .INIT_0C(256'h0000000000000000000000000000000000000000000000000000000000000000),
    .INIT_0D(256'h0000000000000000000000000000000000000000000000000000000000000000),
    .INIT_0E(256'h0000000000000000000000000000000000000000000000000000000000000000),
    .INIT_0F(256'h0000000000000000000000000000000000000000000000000000000000000000),
    .INIT_10(256'h0000000000000000000000000000000000000000000000000000000000000000),
    .INIT_11(256'h0000000000000000000000000000000000000000000000000000000000000000),
    .INIT_12(256'h0000000000000000000000000000000000000000000000000000000000000000),
    .INIT_13(256'h0000000000000000000000000000000000000000000000000000000000000000),
    .INIT_14(256'h0000000000000000000000000000000000000000000000000000000000000000),
    .INIT_15(256'h0000000000000000000000000000000000000000000000000000000000000000),
    .INIT_16(256'h0000000000000000000000000000000000000000000000000000000000000000),
    .INIT_17(256'h0000000000000000000000000000000000000000000000000000000000000000),
    .INIT_18(256'h0000000000000000000000000000000000000000000000000000000000000000),
    .INIT_19(256'h0000000000000000000000000000000000000000000000000000000000000000),
    .INIT_1A(256'h0000000000000000000000000000000000000000000000000000000000000000),
    .INIT_1B(256'h0000000000000000000000000000000000000000000000000000000000000000),
    .INIT_1C(256'h0000000000000000000000000000000000000000000000000000000000000000),
    .INIT_1D(256'h0000000000000000000000000000000000000000000000000000000000000000),
    .INIT_1E(256'h0000000000000000000000000000000000000000000000000000000000000000),
    .INIT_1F(256'h0000000000000000000000000000000000000000000000000000000000000000),
    .MODE("DP8K"),
    .OCEAMUX("0"),
    .OCEBMUX("0"),
    .REGMODE_A("NOREG"),
    .REGMODE_B("NOREG"),
    .RESETMODE("SYNC"),
    .WRITEMODE_A("WRITETHROUGH"),
    .WRITEMODE_B("WRITETHROUGH"))
    inst_1024x32_sub_000000_027 (
    .addra({addra,3'b111}),
    .addrb({addrb,3'b111}),
    .clka(clka),
    .clkb(clkb),
    .dia({open_n85,open_n86,open_n87,open_n88,dia[31:27]}),
    .dib({open_n89,open_n90,open_n91,open_n92,dib[31:27]}),
    .rsta(rsta),
    .rstb(rstb),
    .wea(wea),
    .web(web),
    .doa({open_n95,open_n96,open_n97,open_n98,doa[31:27]}),
    .dob({open_n99,open_n100,open_n101,open_n102,dob[31:27]}));

endmodule 
